Frank-Bemelman/radioglobe-esp32-2025/source/squareline/assets/worldmap_bw_360x180.png

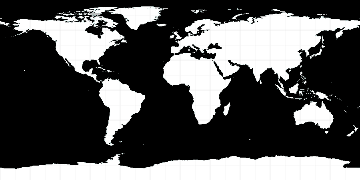
source/squareline/assets/worldmap_bw_360x180.png
