Frank-Bemelman/radioglobe-esp32-2025/source/arduino/RadioGlobe-Display-V4/LVGL_Driver.cpp

/*****************************************************************************
  | File        :   LVGL_Driver.c
  
  | help        : 
    The provided LVGL library file must be installed first
******************************************************************************/
#include "LVGL_Driver.h"

//lv_disp_drv_t disp_drv;
lv_disp_drv_t* disp_drv_ptr = NULL;
// uint8_t disp_drv_safety_buffer[64]; // Dit vangt elke mogelijke overflow gegarandeerd op - ik vertrouw disp_drv niet -> eruit, nu eea weer goed loopt - als extra check of dit verschil maakte

static lv_disp_draw_buf_t draw_buf;
void* buf1 = NULL;
void* buf2 = NULL;
// static lv_color_t buf1[ LVGL_BUF_LEN ];
// static lv_color_t buf2[ LVGL_BUF_LEN ];
// static lv_color_t* buf1 = (lv_color_t*) heap_caps_malloc(LVGL_BUF_LEN, MALLOC_CAP_SPIRAM);
// static lv_color_t* buf2 = (lv_color_t*) heap_caps_malloc(LVGL_BUF_LEN, MALLOC_CAP_SPIRAM);
    
lv_disp_drv_t *current_disp_drv = NULL; // 28JUL26 20:23

/* Serial debugging */
void Lvgl_print(const char * buf)
{
    // Serial.printf(buf);
    // Serial.flush();
}

/*  Display flushing 
    Displays LVGL content on the LCD
    This function implements associating LVGL data to the LCD screen
*/
void Lvgl_Display_LCD( lv_disp_drv_t *disp_drv, const lv_area_t *area, lv_color_t *color_p )
{ // 28JUL26 20:23 store current driver for VSYNC callback usage
  current_disp_drv = disp_drv; 
  
  // 28JUL26 20:53 replace LCD_addWindow for official esp recommendations
  esp_lcd_panel_draw_bitmap(panel_handle, area->x1, area->y1, area->x2 + 1, area->y2 + 1, color_p);
  
  // 28JUL26 20:53 commented out
  // LCD_addWindow(area->x1, area->y1, area->x2, area->y2, (uint8_t *)color_p);


  
  // 28JUL26 20:23moved to example_on_vsync_event
  //lv_disp_flush_ready( disp_drv );
}
/*Read the touchpad*/
void Lvgl_Touchpad_Read( lv_indev_drv_t * indev_drv, lv_indev_data_t * data )
{
  Touch_Read_Data();
  if (touch_data.points != 0x00) {
    data->point.x = touch_data.x;
    data->point.y = touch_data.y;
    data->state = LV_INDEV_STATE_PR;
// FRANK disabled    printf("LVGL : X=%u Y=%u points=%d\r\n",  touch_data.x , touch_data.y,touch_data.points);
  } else {
    data->state = LV_INDEV_STATE_REL;
  }
  if (touch_data.gesture != NONE ) {    
  }
  touch_data.x = 0;
  touch_data.y = 0;
  touch_data.points = 0;
  touch_data.gesture = NONE;
}
void example_increase_lvgl_tick(void *arg)
{
    /* Tell LVGL how many milliseconds has elapsed */
    lv_tick_inc(EXAMPLE_LVGL_TICK_PERIOD_MS);
}
void Lvgl_Init(void)
{
  lv_init();
  esp_lcd_rgb_panel_get_frame_buffer(panel_handle, 2, &buf1, &buf2);                                          
  lv_disp_draw_buf_init( &draw_buf, buf1, buf2, ESP_PANEL_LCD_WIDTH * ESP_PANEL_LCD_HEIGHT);           

  /*Initialize the display*/
  disp_drv_ptr = (lv_disp_drv_t*)malloc(sizeof(lv_disp_drv_t));
  lv_disp_drv_init(disp_drv_ptr);
  //lv_disp_drv_init( &disp_drv );
  
  /*Change the following line to your display resolution*/
  disp_drv_ptr->hor_res = LCD_HEIGHT;
  disp_drv_ptr->ver_res = LCD_WIDTH;
  disp_drv_ptr->flush_cb = Lvgl_Display_LCD;
  disp_drv_ptr->full_refresh = 1;                    /**< 1: Always make the whole screen redrawn*/
  disp_drv_ptr->draw_buf = &draw_buf;

  
  //disp_drv.hor_res = LCD_HEIGHT;
  //disp_drv.ver_res = LCD_WIDTH;
  //disp_drv.flush_cb = Lvgl_Display_LCD;
  //disp_drv.full_refresh = 1;                    /**< 1: Always make the whole screen redrawn*/
  //disp_drv.draw_buf = &draw_buf;

  lv_disp_drv_register(disp_drv_ptr);
  //lv_disp_drv_register( &disp_drv );

  /*Initialize the (dummy) input device driver*/
  static lv_indev_drv_t indev_drv;
  lv_indev_drv_init( &indev_drv );
  indev_drv.type = LV_INDEV_TYPE_POINTER;
  indev_drv.read_cb = Lvgl_Touchpad_Read;
  lv_indev_drv_register( &indev_drv );

  /* Create simple label */
  lv_obj_t *label = lv_label_create( lv_scr_act() );
  lv_label_set_text( label, "Hello Ardino and LVGL!");
  lv_obj_align( label, LV_ALIGN_CENTER, 0, 0 );

  const esp_timer_create_args_t lvgl_tick_timer_args = {
    .callback = &example_increase_lvgl_tick,
    .name = "lvgl_tick"
  };
  esp_timer_handle_t lvgl_tick_timer = NULL;
  esp_timer_create(&lvgl_tick_timer_args, &lvgl_tick_timer);
  esp_timer_start_periodic(lvgl_tick_timer, EXAMPLE_LVGL_TICK_PERIOD_MS * 1000);

}

extern SemaphoreHandle_t lvgl_mutex;

void Lvgl_Loop(void)
{ if (xSemaphoreTake(lvgl_mutex, pdMS_TO_TICKS(50)) == pdTRUE)  // maybe not - crashes worldmap when touched multiple times
  { lv_timer_handler(); /* let the GUI do its work */
    xSemaphoreGive(lvgl_mutex); // Geef de sleutel direct weer terug
  }
  vTaskDelay(pdMS_TO_TICKS(1)); // let's try again 21JUL26
}
