Frank-Bemelman/radioglobe-esp32-2025/source/arduino/RadioGlobe-Display-V4/database.ino

// functions for database of radio stations
// makes use of stations.json file stored on SD card

#include "FS.h"
#include "SD_MMC.h"
#include "database.h"
#include "countrycodes.h"

#include <ctype.h>


bmpfile StationsMap;  // to maintain a quick lookup map of available directories     
//bmpfile NauticMap;    // to have a map of water vs land that have actual timezones according to google
stations_arraybin Stations;



char rolldata[(64+2)*MAX_STATIONS];


void listDir(fs::FS &fs, const char *dirname, uint8_t levels) {
  Serial.printf("Listing directory: %s\n", dirname);

  File root = fs.open(dirname);
  if (!root) {
    Serial.println("Failed to open directory");
    return;
  }
  if (!root.isDirectory()) {
    Serial.println("Not a directory");
    return;
  }

  File file = root.openNextFile();
  while (file) {
    if (file.isDirectory()) {
      Serial.print("  DIR : ");
      Serial.println(file.name());
      if (levels) {
        listDir(fs, file.path(), levels - 1);
      }
    } else {
      Serial.print("  FILE: ");
      Serial.print(file.name());
      Serial.print("  SIZE: ");
      Serial.println(file.size());
    }
    file = root.openNextFile();
  }
}



// REBUILD DATABASE BUTTON
void RebuildDatabase(lv_event_t * e)
{ if(isLongPressed(e)==5)
  { beepforMs(1000);
    bCheckDatabase = true;
  }
}

// create a directory structure per NS degree and EW degree
// in theory 64800 files to store
// ./N/N<digit/10>/<digit%10>/E<digit/10>/<digit%10>
// ./N/N<digit/10>/<digit%10>/W<digit/10>/<digit%10>
// ./S/S<digit/10>/<digit%10>/E<digit/10>/<digit%10>
// ./S/S<digit/10>/<digit%10>/W<digit/10>/<digit%10>
// each directory containing filenames like N24W25urls.txt containing list of stations for that coordinate

void BuildDatabaseNow(void)
{ uint16_t timeout = 5;
  char content[128];
  char filename[32];

  Serial.printf("BuildDatabaseNow()\n");

  lv_label_set_text(ui_Database_Output_File, "");
  lv_obj_clear_flag(uic_RebuildDatabase, LV_OBJ_FLAG_HIDDEN);
  lv_obj_clear_flag(uic_RebuildDatabaseButtonText, LV_OBJ_FLAG_HIDDEN);
  lv_obj_add_state(uic_RebuildDatabase, LV_STATE_DISABLED);
  lv_obj_add_flag(uic_HomeButton3, LV_OBJ_FLAG_HIDDEN);
  //lv_label_set_text(ui_MapBanner, "All\nThose\nBeautiful\nInternet\nRadio\nStations\nAround\nThe\nWorld\n");

  if(Puck_SD_GB == 0)
  { lv_label_set_text(ui_Database_Dir_Path, "No SD Card Found!");
    lv_refr_now(NULL); 
    delay(1000);
    while(timeout)
    {  delay(1000);
       sprintf(content, "leaving in %d seconds", timeout);
       lv_label_set_text(ui_Database_Dir_Path, content);
       lv_refr_now(NULL); 
       timeout --;
    }
    delay(1000);
    lv_scr_load(ui_Home); 
    lv_label_set_text(ui_Database_Dir_Path, "");
  }
  else
  { lv_label_set_text(ui_Database_Dir_Path, "SD Card Found!");
    lv_refr_now(NULL); 
    strcpy(filename, "/stations150K.json"); // don't fortget the forward slash
    ReadDatabase(SD_MMC, filename); // don't fortget the forward slash
    WriteStationsBitmapFile(SD_MMC, "/stationsmap.bmp");
    Serial.println("Database rebuild done");
  }
  Serial.println("End BuildDatabaseNow()");
  bCheckDatabase = false;
}

void ReadDatabase(fs::FS &fs, char *filename)
{ char sometext[128];
  char oneline[128];
  char outputfilename[64];
  char dirpath[64];
  char *p;
  size_t bytesread;
  uint32_t filesize = 0;
  uint32_t fileposition = 0;
  uint16_t percentagedone;
  uint32_t startMillis = millis();  
  uint32_t currentMillis;
  uint16_t parsefase = 0;
  uint32_t urlcount = 0;
  uint32_t filecount = 0;
  float floatn;
  float floate;
  int16_t ns=0;
  int16_t ew=0;
  File urls;

  if(1)
  { File root = fs.open(filename, FILE_READ);
    if (!root) 
    { sprintf(sometext, "Failed To Open %s", filename);
      lv_label_set_text(ui_Database_Dir_Path, sometext);
      lv_refr_now(NULL);
      Serial.println(sometext);
      delay(2000); 
      lv_obj_clear_state(uic_RebuildDatabase, LV_STATE_DISABLED);
      lv_obj_clear_flag(uic_HomeButton3, LV_OBJ_FLAG_HIDDEN);
      return;
    }
    sprintf(sometext, "Succes opening %s", filename);
    lv_label_set_text(ui_Database_Dir_Path, sometext);
    lv_refr_now(NULL); 
    delay(2000); 
  
    filesize = root.size(); // used for progress percentage calculation
    // Serial.printf("filesize of %s is %ld\n", filename, filesize);

    lv_obj_set_pos(uic_MapCursor, ew, -ns);
    // Start the animation on the map
    //lv_obj_clear_state(uic_MapBanner, LV_STATE_DISABLED);
    lv_obj_clear_state(uic_MapCursor, LV_STATE_DISABLED);

    // invalidate map red dots, make it blank
    memset(StationsMap.pixeldata, 0x0, sizeof(StationsMap.pixeldata));

    while(root.available())//  && urlcount < 500)
    { bool UpdateGrapics;
      currentMillis = millis();
      if (currentMillis - startMillis >= 1000)  // every 5S screen update
      { startMillis = currentMillis;
        UpdateGrapics = true;
        fileposition = root.position();
        percentagedone = fileposition * 100 / filesize;
        sprintf(sometext, "Done %d%% urls=%ld", percentagedone, urlcount);
        lv_label_set_text(ui_Database_Progress, sometext);
        lv_refr_now(NULL); 
      }

      bytesread = root.readBytesUntil(0x0a, oneline, sizeof(oneline)-1);
      oneline[bytesread]=0;
      //Serial.printf("bytesread= %d lineread = %s\n", bytesread, oneline);
      switch(parsefase)
      { case 0:
          if((p = strstr(oneline, "\": {")) != NULL) // city,country
          { // example
            //    "Winston-Salem,US": {
            // results in: Winston-Salem_US.txt  
            if((p=strchr(oneline, '\"'))!=NULL)
            { strcpy(outputfilename, p+1);
              if((p=strchr(outputfilename, '\"')) != NULL)*p=0;
              if((p=strchr(outputfilename, ',')) != NULL)*p='_';
              // seen a city, country entry like this "Biel/Bienne,CH": {
              // which causes havoc when filesystem sees this as a directory path
              // fix by replacing the / for a -
              if((p=strchr(outputfilename, '/')) != NULL)*p='-';
              strcat(outputfilename, ".txt");
              Serial.println(outputfilename);
            }
            else strcpy(outputfilename, "noname.txt");
            parsefase = 1;
          }
          break;
        case 1:
          if((p = strstr(oneline, "\"n\": ")) != NULL)
          { //Serial.println(p);
            sscanf(&p[5], "%f", &floatn);
            if(floatn>0)ns=(int)(floatn+0.5);
            else ns=(int)(floatn-0.5);
            parsefase = 2;
          }        
          break;
        case 2: // create directory
          if((p = strstr(oneline, "\"e\": ")) != NULL)
          { //Serial.println(p);
            sscanf(&p[5], "%f", &floate);
            if(floate>0)ew=(int)(floate+0.5);
            else ew=(int)(floate-0.5);
            sprintf(dirpath, "/%c/%d/%d/%c/%d/%d", (ns<0)?'S':'N', abs(ns)/10, abs(ns)%10, (ew<0)?'W':'E', abs(ew)/10, abs(ew)%10);
            //Serial.println(dirpath);
            CreateAllDirInPath(fs, dirpath);
            SetPixelInMap(ns, ew);
            if(UpdateGrapics)lv_obj_set_pos(uic_MapCursor, ew, -ns);
            parsefase = 3;
          }
          break;
        case 3:  // create file
          if((p = strstr(oneline, "\"urls\": [")) != NULL) // start of list
          { sprintf(sometext, "Folder %s", dirpath);
            if(UpdateGrapics)lv_label_set_text(ui_Database_Dir_Path, sometext);
            if(UpdateGrapics)lv_label_set_text(ui_Database_Output_File, outputfilename);
            sprintf(sometext, "/%s/%s", dirpath, outputfilename);
            // SD_MMC.remove(sometext); // delete old file
            urls = SD_MMC.open(sometext, FILE_WRITE);
            filecount++;
            parsefase = 4;
          }
          break;
        case 4:  
          if((p = strstr(oneline, "\"name\": ")) != NULL) // name found
          { //Serial.println(p);
            urls.println(p);  // write name to file 
            parsefase = 5;
          }
          if((p = strstr(oneline, "]")) != NULL) // end of file reached
          { //Serial.println(p);
            urls.close();
            parsefase = 0;
          }
          break;
        case 5:  
          if((p = strstr(oneline, "\"url\": ")) != NULL) // url found
          { //Serial.println(p);
            urls.println(p);  // write to file 
            parsefase = 6;
          }
          break;
        case 6:  
          sprintf(sometext, "\"gps\": \"%f,%f\"", floatn, floate); // write gps to file
          urls.println(sometext);  
          urlcount++;
          parsefase = 4;
          break;

        default:
          break;  
      }
    }  

    urls.close();
    root.close();
    //lv_obj_add_state(uic_MapBanner, LV_STATE_DISABLED); 
    lv_obj_add_state(uic_MapCursor, LV_STATE_DISABLED); 

    percentagedone = 100;
    sprintf(sometext, "Done %d%% urls=%ld", percentagedone, urlcount);
    lv_label_set_text(ui_Database_Progress, sometext);
    sprintf(sometext, "%d Locations Created", filecount);
    lv_label_set_text(ui_Database_Dir_Path, sometext);
    lv_refr_now(NULL); 

  }

   //tellme();

  lv_obj_clear_state(uic_RebuildDatabase, LV_STATE_DISABLED);
  lv_obj_clear_flag(uic_HomeButton3, LV_OBJ_FLAG_HIDDEN);
  
  Serial.println("Database rebuild completed!");
}



void CreateAllDirInPath(fs::FS &fs, char *path) 
{ char pathcopy[64];
  char *s;
  char *d;
  File root;
  s = path;
  d = pathcopy;

  

  //Serial.printf("Create these directories %s\n", path);
  *d++ = *s++; // copy first '/'
  while(*s)
  { while(*s)
    { *d++ = *s++; // copy intil '/' found
      if(*s == '/')
      { break;
      }
    }
    *d = 0; // terminate string

    //Serial.printf("Full path %s\n", path);
    //Serial.printf("Try to open directory %s!\n", pathcopy);
    root = fs.open(pathcopy);
    if(!root) 
    { //Serial.printf("Failed to open directory %s so make it!\n", pathcopy);
      if(SD_MMC.mkdir(pathcopy))
      { //Serial.printf("%s created\n", pathcopy);
      }
      //else Serial.printf("%s creation error\n", pathcopy);
    }
    *d = *s; // *s is '/' in case more directories todo
    // Serial.printf("*s = %d\n", (int)*s);
  }
}      

#define EXPAND_STOP 10 // was 45 - original radioglobe by Jude Pullen uses 2 degrees expansion, too small imo
bool SnapToNearestStation(int16_t for_ns, int16_t for_ew, int16_t *to_ns, int16_t *to_ew, uint16_t hit_count)
{ // convert/round to whole degrees to be used for finding a position with an existing directory path and station file
  int16_t ns;
  int16_t ew;
  int16_t expand;
  int16_t try_ns;
  int16_t try_ew;
  int16_t try_ltx;
  int16_t try_lty;
  int16_t try_rbx;
  int16_t try_rby;
  uint16_t match_count = 0;
  int16_t expand_stop;

  
  ns = for_ns;
  ew = for_ew;
  
  Serial.printf("[Database.ino ~ 352] SnapToNearestStation NS = %d  EW = %d\n", ns, ew);
  if(DisplaySettings.expand_search>100)DisplaySettings.expand_search=100;
  expand_stop = DisplaySettings.expand_search+1;
  Serial.printf("expand_stop = %d\n", expand_stop);
  
  // start at the exact position
  // expand as needed by 1 degree
  // hit_count parameter to find 1st or 2nd or 3rd pixel in map
  // to be used if 1st or next pixel gives a dissapointing small amount of stations

  try_ns = ns;
  try_ew = ew;
  expand = 0;

  
  while((expand < expand_stop) && (match_count!=hit_count))
  { // define the square to scan
    try_lty = ns - expand;
    try_ltx = ew - expand;
    try_rby = ns + expand;
    try_rbx = ew + expand;

    if(TestPixelInMap(try_ns, try_ew) && match_count==0)
    { match_count++;
      expand++;
    }
    else // loop around
    { try_ns = try_lty; 
      try_ew = try_ltx; 
      while(try_ew<try_rbx && (match_count!=hit_count)) // go right 
      { try_ew++;
        if(TestPixelInMap(try_ns, try_ew))
        { match_count++;
        }  
      }
      while(try_ns<try_rby && (match_count!=hit_count)) // go down 
      { try_ns++;
        if(TestPixelInMap(try_ns, try_ew))
        { match_count++;
        }  
      }
      while(try_ew>try_ltx && (match_count!=hit_count)) // go left 
      { try_ew--;
        if(TestPixelInMap(try_ns, try_ew))
        { match_count++;
        }  
      }
      while(try_ns>try_lty && (match_count!=hit_count)) // go up 
      { try_ns--;
        if(TestPixelInMap(try_ns, try_ew))
        { match_count++;
        }  
      }
      expand++;
    }
  }

  if(expand >= expand_stop)
  { Serial.printf("No station with expand %d -> NS -> %d WE -> %d\n", expand, try_ns, try_ew);
    return false; 
  }
  Serial.printf("Stations found within expand %d -> NS -> %d WE -> %d\n", expand, try_ns, try_ew);
  *to_ns = try_ns;
  *to_ew = try_ew;
  return true;
}


// find stations at current calibrated position
int32_t search_mS;
void FindNewStation(void)
{ bool dirscan = true;
  bool dirfound = false;
  int16_t ns;
  int16_t ew;
  int16_t dir_ns;
  int16_t dir_ew;
  int16_t center;
  char oneline[128];
  size_t bytesread;
  char *p;

  // results from SnapToNearestStation()
  bool mapfind = false;
  int16_t mapfind_ns;
  int16_t mapfind_ew;

  char dirpath[64];
  File root;
  File file;
  char content[64];
  
  
  search_mS = 0;
 
  // convert to whole degrees to be used for finding directory path to url file
  ns = (DataFromDisplay.ns_cal+5)/10; // from tenths of degrees to whole degrees
  ew = (DataFromDisplay.ew_cal+5)/10; // from tenths of degrees to whole degrees

  Stations.count = 0;
  Stations.requested -1;
  char firstcountrycode[3] = ""; // near borders, different countries can be in the directory, decided to stick with the country first found, to avoid a mixed list

  lv_label_set_text(ui_Station_Name, "");
  lv_label_set_text(ui_Home_City, "");
  lv_obj_add_flag(ui_Home_Flag, LV_OBJ_FLAG_HIDDEN); 
  lv_label_set_text(ui_Home_Country, "");
  // also on clock, in case we play the globe while clock is shown
  lv_obj_add_flag(ui_ClockFlag, LV_OBJ_FLAG_HIDDEN); 
  lv_label_set_text(ui_Clock_Country, "");
  lv_refr_now(NULL); // show immediately
  

  search_mS = millis();

  //nieuw, probeer minimaal 10 stations te vinden, blijf witte pixels zoeken
  uint16_t hitcount = 0;
  while(Stations.count < 10 && hitcount<10)
  { hitcount++;
    mapfind = SnapToNearestStation(ns, ew, &mapfind_ns, &mapfind_ew, hitcount);
    if(mapfind == 0)
    { // game over
      break;
    }
    CollectStationsAtGps(mapfind_ns, mapfind_ew, firstcountrycode);
    Serial.printf("Collecting Attempt %d gave %d stations in %ld mS\n", hitcount, Stations.count, (millis() - search_mS));
  }

  
  Serial.printf("End search -> %ld\n", millis() - search_mS);
  
  if(Stations.count)
  { //sprintf(content, "%d Stations Found", Stations.count);
    //lv_label_set_text(ui_Station_Name, content);
    
    AddToQueueForGlobe("Reset Your DataFromGlobe.D_QueueStationIndex to -1", MESSAGE_NEW_LIST_LOADED);
    
    // pick a random station from the list
    uint16_t random_station; 
    random_station = random(0,Stations.count);
    
    Stations.connect_attempts = 0;
    //ForceGlobeStationGPSupdate = true; 
    //AddStationToQueueForGlobe(random_station);
  }  
  else
  { lv_label_set_text(ui_Station_Name, "No Stations Found");
    // normally, timezone is requested for the station that is requested
    // if no stations are found, set the timezone according to the coordinates from the globe
    Stations.requested = -1; 
    AddStationToQueueForGlobe(-1); // no new station to play really, but will trigger timezone/geolocation requests
  }

  // dump to serial port
  //for(int n = 0; n<Stations.count; n++)
  //{ Serial.printf("[%d] N=%s\nU=%s\n", n, Stations.StationNUG[n].name, Stations.StationNUG[n].url);
  //}

  Stations.connect_attempts = 0;
  ScrollNeedsReload = true;
}

void CollectStationsAtGps(int16_t mapfind_ns, int16_t mapfind_ew, char *firstcountrycode)
{ File root;
  File file;
  char dirpath[64];
  char content[64];
  int16_t dir_ns;
  int16_t dir_ew;
  char oneline[128];
  size_t bytesread;
  char *p;
  char town[32] = "";
  char countrycode[3] = "";
  char countryname[50] ="";
        

  
  if(Puck_SD_GB)
  { dir_ns = mapfind_ns;
    dir_ew = mapfind_ew;
    sprintf(dirpath, "/%c/%d/%d/%c/%d/%d", (dir_ns<0)?'S':'N', abs(dir_ns)/10, abs(dir_ns)%10, (dir_ew<0)?'W':'E', abs(dir_ew)/10, abs(dir_ew)%10);
    Serial.println(dirpath);
    //lv_label_set_text(ui_Station_Title, dirpath);
    //lv_refr_now(NULL); 

    root = SD_MMC.open(dirpath);
    if (!root) 
    { Serial.println("Failed to open directory");
      return;
    }
    
    file = root.openNextFile();

    while (file) 
    { if(!file.isDirectory()) 
      { //Serial.print("STATIONS FILE: ");
        //Serial.print(file.name());
        //Serial.print(" FILE SIZE: ");
        //Serial.println(file.size());

        // while (file && Stations.count<(MAX_STATIONS-1))
        // dit gaat op tilt, met name bij de reload scroll als meer dan ?? stations, zeker geen 100 of 150 mogelijk 
        // dus even naar 25 max

        Serial.printf("File with stations (=%d) opened in %ld mS\n", Stations.count, (millis() - search_mS));

        if (Stations.count >= MAX_STATIONS) 
        { file.close();
          break; // done, get out og here
        }
        
        if(Stations.count==0)
        { lv_label_set_text(ui_Station_Title, file.name());
          lv_refr_now(NULL); 
        }  
        
        strcpy(town, file.name());
        // filenames are constructed from name of town, underscore, and 2 letter country code, like -> Amsterdam_NL.txt
        if((p=strchr(town, '_')) != NULL)
        { *p++ = 0;
          //Serial.printf("sizeof(Countrylist) = %ld\n", sizeof(CountryList) / sizeof(country_info));
          strncpy(countrycode, p, 2);
          countrycode[2]=0;

          if(strlen(firstcountrycode) == 0)strcpy(firstcountrycode, countrycode);

          if(!FindCountryNameByCode(countryname, countrycode))
          { Serial.printf("Not a valid countrycode %s !!!!!!!!!!!!!!!\n", countrycode);
          }
          Serial.printf("Found country: <%s>\n", countryname);
        }


        if(strcmp(firstcountrycode, countrycode) == 0) // same country
        {
          while(file.available() && Stations.count<MAX_STATIONS)
          { bytesread = file.readBytesUntil(0x0a, oneline, sizeof(oneline)-1);
            oneline[bytesread]=0;
            if((p = strrchr(oneline, '\"')) != NULL)*p=0; // get rid of the last "
            // Serial.println(oneline);
            if((p = strstr(oneline, "\"name\": \"")) != NULL)
            { // example:  "name": "Dr P4 Syd"
              // Serial.println(p+9);
              p+=9; // jump forward to start of name
              *(p+31)=0; 
              strcpy(Stations.StationNUG[Stations.count].name, p);
            }  
            else if((p = strstr(oneline, "\"url\": \"")) != NULL)
            { // example:  "url": "https://stream.radio-fratz.de/stream_high.mp3"
              // Serial.println(p+8);
              p+=8; // jump forward to start of url
              strcpy(Stations.StationNUG[Stations.count].url, p);
            }  
            else if((p = strstr(oneline, "\"gps\": \"")) != NULL)
            { // Serial.println(p+8);
              p+=8; // jump forward to start of gps coordinates
              sscanf(p, "%f,%f", &Stations.StationNUG[Stations.count].gps_ns, &Stations.StationNUG[Stations.count].gps_ew);

              strcpy(Stations.StationNUG[Stations.count].town, town);
              strcpy(Stations.StationNUG[Stations.count].countrycode, countrycode);
              strcpy(Stations.StationNUG[Stations.count].countryname, countryname);

              // play first one found, for snappy feeling
              if(Stations.count==0)
              { ForceGlobeStationGPSupdate = true; 
                AddStationToQueueForGlobe(Stations.count);
                while(ToGlobe.QueueCnt)loop_esp_now(); // send everything out immediately 
              }  

              // in all honesty, ignore if country not the same as first one found and also ignore this url if already in list
              if(strcmp(firstcountrycode, countrycode) == 0) // same country
              { //Serial.printf("%s same as %s\n", firstcountrycode, countrycode);
                if(CheckIfUniqueUrl())
                { Stations.count++;
                  Serial.printf("Station %d (country %s )found in %ld mS\n", Stations.count, Stations.StationNUG[Stations.count].countryname, (millis() - search_mS));
                }  
              }
              else
              { Serial.printf("%s differs from %s\n", firstcountrycode, countrycode);
              }
            }
          } 
        }
      }
      file.close();
      file = root.openNextFile();
    } 
    root.close();
  }
}

bool CheckIfUniqueUrl(void)
{ uint16_t idx=0;
  if(!Stations.count)return true;
  while(idx<Stations.count)
  { if(strcmp(Stations.StationNUG[Stations.count].url, Stations.StationNUG[idx].url)==0)return false; // url already in list of stations
    idx++;
  }
  return true;
}

void SetPixelInMap(int16_t ns, int16_t ew)
{ // ew varies between -180 and 180
  // -180 to be stored in [359]
  ew += 180;  // convert -180 to 179 range to 0-359
  ns += 90;   // convert -90 to 90 range to 0-180
  if(ns>179)ns=179;
  if(ew>359)ew-=360;
  StationsMap.pixeldata[((180-ns)*48)+(ew/8)] |= 0x80>>(ew%8); //48 bytes, rounded up from 45 to get a 4-byte multiple
}

bool TestPixelInMap(int16_t ns, int16_t ew)
{ // ew varies between -180 and 179
  // ns varies between 90 and -89
  // -180 to be stored in [359]
  ew += 180;  // convert -180 to 179 range to 0-359
  ns += 90;   // convert -90 to 90 range to 0-180
  if(ns>179)ns=179;
  if(ew>359)ew-=360;
  if(ns<1)return false;
  if(ew<1)return false;
  
  //Serial.printf("Pixeltest ns=%d ew=%d %02X vs %02X\n", ns, ew, (uint16_t)StationsMap.pixeldata[((180-ns)*48)+(ew/8)], (uint16_t)(0x80>>(ew%8)));
  if(StationsMap.pixeldata[((180-ns)*48)+(ew/8)] & (0x80>>(ew%8)))return true;
  return false;
}



void tellme(void)
{ Serial.println(StationsMap.bmpheader.filler);
  Serial.println(StationsMap.bmpheader.type);
  Serial.println(StationsMap.bmpheader.size);
  Serial.println(StationsMap.bmpheader.reserved1);
  Serial.println(StationsMap.bmpheader.reserved2);
  Serial.println(StationsMap.bmpheader.offset);
  Serial.println(StationsMap.bmpheader.dib_header_size);
  Serial.println(StationsMap.bmpheader.width_px);
  Serial.println(StationsMap.bmpheader.height_px);
  Serial.println(StationsMap.bmpheader.num_planes);
  Serial.println(StationsMap.bmpheader.bits_per_pixel);
  Serial.println(StationsMap.bmpheader.compression);
  Serial.println(StationsMap.bmpheader.image_size_bytes);
  Serial.println(StationsMap.bmpheader.x_resolution_ppm);
  Serial.println(StationsMap.bmpheader.y_resolution_ppm);
  Serial.println(StationsMap.bmpheader.num_colors);
  Serial.println(StationsMap.bmpheader.important_colors);

  int n;
  int w;
  for(n=0;n<180;n++)
  { for(w=0;w<45;w++)
    { Serial.printf("%02x", (uint16_t)StationsMap.pixeldata[(n*48)+w]); //48 bytes, rounded up from 45 to get a 4-byte multiple
    }
    Serial.printf("\n");
  }
}


static uint32_t startMillis;
static uint32_t currentMillis;


void RadioGlobeClick(lv_event_t * e)
{ int16_t clicktime;
  lv_event_code_t event_code = lv_event_get_code(e);

  clicktime = isLongPressedV2(e);
  //Serial.printf("RadioGlobeClick() clicktime = %d\n", clicktime);
  
  if(clicktime==0) // normal click
  { if(!bMusicMode)
    { Serial.printf("!bMusicMode RadioGlobeClick() Stations.count = %d\n", Stations.count);
      if(Stations.count == 0)
      { SetFlag("xxxx");
        lv_obj_add_flag(uic_Home_City, LV_OBJ_FLAG_HIDDEN); // hide city name until new country code is received
        lv_obj_add_flag(uic_Home_Country, LV_OBJ_FLAG_HIDDEN); // hide country name until new country code is received

        //lv_label_set_text(ui_Station_Name, "Searching..."); // pointless, searching goes so fast you won't see this
        lv_label_set_text(ui_Station_Title, "");
        lv_obj_add_flag(ui_ledconnect, LV_OBJ_FLAG_HIDDEN); 
        lv_refr_now(NULL); 
        FindNewStation();
        ReloadScroll();
      }
    }
    else
    { //Serial.printf("bMusicMode RadioGlobeClick() Stations.count = %d\n", Stations.count);
      ReloadScroll();
    }
    beepforMs(50);
    lv_scr_load(ui_StationSelectScreen);
    startMillis = millis(); 
    Serial.printf("RadioGlobeClick() return\n");
  }  

  if(clicktime==5 && DisplaySettings.globe_sd_gb!=0) // long press, toggle between radio/music mode
  { //Serial.printf("RadioGlobeClick clicktime==5 LV_EVENT_LONG_PRESSED_REPEAT \n");
    if(!bMusicMode)
    { //Serial.printf("Radio -> Music Mode LV_EVENT_LONG_PRESSED_REPEAT \n");
      beepforMs(50);
      SetLed(0,0); SetLed(1,0); SetLed(2,0); SetLed(3,0);
      lv_label_set_text(ui_Station_Name, "");
      lv_label_set_text(ui_Status_Line, "READING SD CARD");
      lv_label_set_text(ui_Station_Title, "");
      lv_obj_add_flag(ui_ledconnect, LV_OBJ_FLAG_HIDDEN); 
      AddToQueueForGlobe("", MESSAGE_GLOBE_PLAY_SD); // instructs the globe to prepare a list of songs from the SD card
      lv_obj_clear_flag(ui_Jukebox, LV_OBJ_FLAG_HIDDEN);
      lv_obj_add_flag(ui_Home_City, LV_OBJ_FLAG_HIDDEN); 
      lv_obj_add_flag(ui_Home_Flag, LV_OBJ_FLAG_HIDDEN); 
      lv_obj_add_flag(ui_Home_Country, LV_OBJ_FLAG_HIDDEN);


      bMusicMode = true;
    } 
    else
    { // back to radio
      //Serial.printf("Music -> Radio Mode LV_EVENT_LONG_PRESSED_REPEAT \n");
      lv_obj_add_flag(ui_Jukebox, LV_OBJ_FLAG_HIDDEN);
      beepforMs(50);
      bMusicMode = false;
      FindNewStation();
      ReloadScroll();
    } 
  }
}

void ReloadScroll(void)
{ uint16_t len;
  uint16_t space;
  uint16_t n;
  char *p;

  if(!ScrollNeedsReload)return;
  ScrollNeedsReload = false;
  space = sizeof(rolldata);
  if(bMusicMode)strcpy(rolldata, "No Files");
  else strcpy(rolldata, "No Stations");
  lv_label_set_text(ui_StationRollerSelected, "0-0");
  lv_roller_set_selected(uic_StationRoller, 0, LV_ANIM_ON);

  for(n = 0; n<Stations.count; n++)
  { if((len = strlen(Stations.StationNUG[n].name))>0)
    { //Serial.printf("n=%d space=%d len=%d\n", n, space, len);
      //Serial.printf("N=%s U=%s\n", Stations.StationNUG[n].name, Stations.StationNUG[n].url);
      //Serial.printf("space = %d\n", space);
      if((space-len)>2)
      { if(n==0)
        { p = rolldata;
        }
        else
        { *p++ = '\n'; // end previous line with a newline
        }  
        strcpy(p, Stations.StationNUG[n].name);
        p += len;
        space -= len;         
      }
      else break;
    }
    else break;
  }
  // Serial.println(rolldata);
  // Serial.println(n);

  if(bMusicMode)
  { lv_label_set_text(ui_StationRollerComment, "Playlist From SD-Card"); // usually says connected to station or something
  }
  else 
  { lv_label_set_text(ui_StationRollerComment, ""); 
  }
  
  lv_label_set_text(uic_StationRollerPlace, "");


  lv_roller_set_options(uic_StationRoller, rolldata, LV_ROLLER_MODE_NORMAL);
  if(Stations.count)
  { char content[32];
    if((Stations.requested >=0) && (Stations.requested<Stations.count))
    { sprintf(content, "%d-%d", Stations.requested+1, Stations.count); // top label 1-150 in stations roller
      Serial.printf("lv_roller_set_selected -> %d\n", Stations.requested);
      lv_roller_set_selected(uic_StationRoller, Stations.requested, LV_ANIM_ON);
    }  
    else 
    { sprintf(content, "0-%d", Stations.count); // top label 1-150 in stations roller
      lv_roller_set_selected(uic_StationRoller, 0, LV_ANIM_ON);
    }
    lv_label_set_text(ui_StationRollerSelected, content);
  }
  Serial.printf("Reload Scroll (%d stations) done.\n", Stations.count);
}






void StationScroll(lv_event_t * e)
{ char content[256];
  static uint16_t RollSelection;
  uint16_t index;
  lv_event_code_t event_code = lv_event_get_code(e);

  // events go from PRESSED while scrolling. Stop&Release results in VALUE_CHANGED + CLICKED
  // another short click gives PRESSED+CHANGED+CLICKED

  index = lv_roller_get_selected(uic_StationRoller);
  sprintf(content, "%d-%d", index+1, Stations.count);
  lv_label_set_text(ui_StationRollerSelected, content); 
  
  if(event_code == LV_EVENT_CLICKED) 
  { index = lv_roller_get_selected(uic_StationRoller);
    currentMillis = millis(); 
    if(currentMillis - startMillis > 250)  //test to distuigish between scrolling and clicking
    { RollSelection = index;
    }
    else // short click
    { Serial.printf("index=%d\n", index);
      if(RollSelection == index)
      { if(index < Stations.count) // just check in case
        { Stations.playing = -1;
          Stations.requested = index; 
          if(!bMusicMode)
          { sprintf(content, "Connecting to %s", Stations.StationNUG[Stations.requested].name);
            lv_label_set_text(ui_StationRollerComment, content); 
            Stations.connect_attempts = 0;
            AddStationToQueueForGlobe(Stations.requested);
          }  
          else AddFileToQueueForGlobe(Stations.requested);
        }
        beepforMs(50);
      }  
      RollSelection = index;
    }
  }
  if(event_code == LV_EVENT_PRESSED) 
  { startMillis = millis();  //get the current "time" (actually the number of milliseconds since the program started)
  }
}

uint16_t AddToScroll(char * songartist)
{ char *p;
  char *q;
  uint16_t len;

  if(Stations.count >= 25)return Stations.count;
  //Serial.printf("songartist -> %s\n", songartist);

  strcpy(Stations.StationNUG[Stations.count].url, songartist);

  // get filename part from url
  // example  /GLOBEMUSIC/HT/Emeline_Michel/Emeline_Michel_-_Reine_De_Coeur_-_2008/08_Yon_Ti_Mo.mp3

  //GLOBE SAYS: PLAYLIST_SONG_ARTIST 60 >/GLOBEMUSIC/FR/Pascal Rogé/Poulenc- Chamber Music/03 Sextet for wind quintet & piano in C major- Prestissimo.mp3<
  //songartist has / -> 03 Sextet for wind quintet & piano in C major- Prestissimo
  //songartist without underscores -> 03 Sextet for wind quintet & piano in C major- Prestissimo
  //songartist split at >-< ->  Prestissimo
  //songartist ended with dots if too long Prestissimo

  if((q=strrchr(songartist, '.'))!= NULL)*q=0; // first, terminate at .mp3

  if((p=strrchr(songartist, '/'))!= NULL) // last '/' in string
  { p++; // skip the '/'
    Serial.printf("songartist had / [%s]\n", p);
  }
  else p = songartist; // start at begin again
  
  RemoveUTF8Unprintables(p); // converts to extended ascii where possible (todo make font table extended too)
  
  // now we have the filename without extension 
  // replace underscores with spaces
  for (int i = 0; p[i] != '\0'; i++) 
  { if (p[i] == '_')  p[i] = ' ';
  }
  Serial.printf("songartist without underscores [%s]\n", p);

  if(isdigit(*p) && isdigit(*(p+1)) && *(p+2)==' ')p+=3; // skip the track number if part of songname
  else if( isalpha(*p) && isdigit(*(p+1)) && isdigit(*(p+2)) && *(p+3)=='-')p+=4; // skip the track number of jukebox files
  else if( isdigit(*p) && isdigit(*(p+1)) && isalpha(*(p+2)))p+=2; // skip numbers as 07A
  else if( isdigit(*p) && isdigit(*(p+1)) && isalpha(*(p+2)))p+=2; // skip numbers as 07A
  Serial.printf("songartist initial cleanup -> [%s]\n", p);
  if(*p=='-')p++; // skip leading '-' if any
  if(*p==' ')p++; // skip leading space if any
  
  // if too long, maybe splice if it is format artist - songtitle format
  if(strlen(p)>20)
  { if((q = strchr(p, '-')) != NULL)
    { q++;
      len = strlen(q);
      memmove(p, q, len);
      p[len]=0;
      Serial.printf("songartist split at >-< [%s]\n", p);
    }
  }
  
  // remove leading spaces just in case
  q = p;
  while(*q != 0 && *q == ' ')q++;
  if(q != p)memmove(p, q, strlen(q) + 1);

  // if still too long, mayby end at full word and add three dots
  while((len = strlen(p))>20)
  { if((q=strrchr(p, ' '))!= NULL) // last space in string
    { strcpy(q, "...");
      Serial.printf("shortened [%s] len was %d\n", p, len);
    }
    else break;
  }

  Serial.printf("songartist ended with dots if too long [%s]\n", p);


  strcpy(Stations.StationNUG[Stations.count].name, p);

  Stations.count++;
  ScrollNeedsReload = true;
  return Stations.count;
}

void StationRollPressed(lv_event_t * e)
{ lv_event_code_t event_code = lv_event_get_code(e);
  //Serial.printf("hey->event=%s\n", "StationRollPressed()");
  StationScroll(e);
}

void StationRollVal(lv_event_t * e)
{ lv_event_code_t event_code = lv_event_get_code(e);
  //Serial.printf("hey->event=%s\n", "StationRollVal()");
  StationScroll(e);
}

void StationRollClicked(lv_event_t * e)
{ lv_event_code_t event_code = lv_event_get_code(e);
  //Serial.printf("hey->event=%s\n", "StationRollClicked");
  StationScroll(e);
}

void RollUp(lv_event_t * e)
{ lv_event_code_t event_code = lv_event_get_code(e);
  //Serial.printf("hey->event=%s\n", "RollUp()");
  //StationScroll(e);
}

void RollDown(lv_event_t * e)
{ lv_event_code_t event_code = lv_event_get_code(e);
  //Serial.printf("hey->event=%s\n", "Rolldown()");
  //StationScroll(e);
}



uint16_t PuckApiRequest; // value to check if arriving result can be discarded, as it could perhaps belongs to previous request

void AddStationToQueueForGlobe(int16_t station)
{ // prepare gps position and url for the station we want to hear and get timezone for
  static char lastgpsrequest[32];
  char message[QUEUEMESSAGELENGTH];
  char content[QUEUEMESSAGELENGTH];

  Stations.requested = station; 
  DataFromDisplay.D_RequestedStation = Stations.requested;
  
  if(station < 0) // no actual station to play really, places with no stations, at sea perhaps, but will trigger timezone/geolocation requests
  { // early setting
    lv_label_set_text(uic_Home_City, "");
    lv_label_set_text(uic_Home_Country, "");
    //on map
    sprintf(content, "GPS NS %2.1f - EW %3.1f", (float)DataFromDisplay.ns_cal/10, (float)DataFromDisplay.ew_cal/10);
    lv_label_set_text(ui_Database_GPS_Position, content);
    lv_obj_set_pos(uic_MapCursor, (int)DataFromDisplay.ew_cal/10 - 16, -(int)DataFromDisplay.ns_cal/10); // moved 16 to left, dot is painted left-top corner?
    lv_label_set_text(ui_Database_Output_File, ""); // remove typical "You are in ..." from map
    
    PuckApiRequest++; // value to check if arriving result can be discarded, as it could perhaps belongs to previous request
    sprintf(content, "%d %f %f %d", station, (float)DataFromDisplay.ns_cal/10, (float)DataFromDisplay.ew_cal/10, PuckApiRequest);
    AddToQueueForGlobe(content, MESSAGE_TIMEZONE_NAME); // will use DataFromDisplay.ns_cal, DataFromDisplay.ew_cal as coordinates
    AddToQueueForGlobe(content, MESSAGE_GET_GEOLOCATION); // will use DataFromDisplay.ns_cal, DataFromDisplay.ew_cal as coordinates
    loop_esp_now(); // send it now, before it gets old
    lv_obj_add_flag(ui_Home_Flag, LV_OBJ_FLAG_HIDDEN); // hide flag
    lv_obj_add_flag(ui_PresetFlag, LV_OBJ_FLAG_HIDDEN);
    SetLed(0,0); SetLed(1,0); SetLed(2,0); SetLed(3,0);

    World.gps_ns = (float)DataFromDisplay.ns_cal/10;
    World.gps_ew = (float)DataFromDisplay.ew_cal/10;
    strcpy(World.CountryName, ""); // we don't know where we are
    
  }
  else if(station<MAX_STATIONS+MAX_FAVORITES)
  { bMusicMode = false;
    DataFromDisplay.D_QueueStationIndex = station;
    Stations.playing = -1;

    if(bPowerStatus == true)
    { sprintf(message, "%s-%s", Stations.StationNUG[station].countrycode, Stations.StationNUG[station].url);
      // send countrycode and station url to globe
      AddToQueueForGlobe(message, MESSAGE_START_THIS_STATION);
    }

    lv_label_set_text(ui_Station_Name, Stations.StationNUG[station].name);
    // easy peasy to postion that led at the end of the station name
    lv_obj_add_flag(ui_ledconnect, LV_OBJ_FLAG_HIDDEN); 
    lv_point_t text_end_point;
    lv_label_get_letter_pos(ui_Station_Name, strlen(Stations.StationNUG[station].name), &text_end_point);
    lv_obj_set_x(ui_ledconnect, (text_end_point.x -200) + 12);
    
//    Serial.printf("x=%d\n",text_end_point );                            

    lv_obj_add_flag(ui_FilePlayProgressBar, LV_OBJ_FLAG_HIDDEN); 
    lv_obj_clear_flag(ui_Status_Line, LV_OBJ_FLAG_HIDDEN); 
    lv_label_set_text(ui_Status_Line, "");
    lv_label_set_text(ui_Station_Title, "");
    lv_refr_now(NULL); 

    if(station<MAX_STATIONS)Stations.connect_attempts++;
    DataFromDisplay.D_StationGpsNS = Stations.StationNUG[station].gps_ns;
    DataFromDisplay.D_StationGpsEW = Stations.StationNUG[station].gps_ew;


    Serial.printf(" -----------------  AddStationToQueueForGlobe() station for country <%s>\n", Stations.StationNUG[station].countrycode);

    // if this country code is our own home country, adjust clock mode for that 
    if(strcmp(Stations.StationNUG[station].countrycode, Stations.StationNUG[(MAX_STATIONS+MAX_FAVORITES+MAX_HOMES-1)].countrycode) == 0)
    { bClockHomeTime = true;
      Home.gps_ns = Stations.StationNUG[(MAX_STATIONS+MAX_FAVORITES+MAX_HOMES-1)].gps_ns;
      Home.gps_ew = Stations.StationNUG[(MAX_STATIONS+MAX_FAVORITES+MAX_HOMES-1)].gps_ew;
      World.gps_ns = 10000; // to prevent clockflagtoggle switch to world mode
      World.gps_ew = 10000; // to prevent clockflagtoggle switch to world mode

    }
    else
    { bClockHomeTime = false;
      World.gps_ns = Stations.StationNUG[station].gps_ns;
      World.gps_ew = Stations.StationNUG[station].gps_ew;
    }

    // check if gps position is a new one
    sprintf(content, "%f %f", Stations.StationNUG[station].gps_ns, Stations.StationNUG[station].gps_ew);
    if(strcmp(lastgpsrequest, content) != NULL || (ForceGlobeStationGPSupdate == true))
    { strcpy(lastgpsrequest, content);
      ForceGlobeStationGPSupdate = false;

      // add station and incrementing PuckApiRequest number
      PuckApiRequest++; // value to check if arriving result can be discarded, as it could perhaps belongs to previous request
      sprintf(content, "%d %s %d", station, lastgpsrequest, PuckApiRequest);
      if(bClockHomeTime)AddToQueueForGlobe(content, MESSAGE_HOME_TIMEZONE_NAME);
      else AddToQueueForGlobe(content, MESSAGE_GET_TIMEZONE_BY_GPS);
      AddToQueueForGlobe(content, MESSAGE_GET_GEOLOCATION_BY_GPS);
      loop_esp_now(); // send it now, before it gets old
    }

    Serial.printf("Flag set early by AddStationToQueueForGlobe() = %s\n", Stations.StationNUG[station].countrycode);

    // show immedeately what is known
    // set flags early - possibly corrected later, when globe thinks it is different 
    SetFlag(Stations.StationNUG[station].countrycode);
    if(bClockHomeTime)
    { strcpy(Home.CountryCode, Stations.StationNUG[station].countrycode); // later used for clock face
      // no country name copied, keep the HOME SWEET HOME text
      //strcpy(Home.CountryName, AllUpperCase(Stations.StationNUG[Stations.requested].countryname)); 
    }
    else
    { strcpy(World.CountryCode, Stations.StationNUG[station].countrycode); // later used for clock face
      strcpy(World.CountryName, Stations.StationNUG[station].countryname); // later used for clock face
    }

    lv_obj_clear_flag(ui_ClockFlag, LV_OBJ_FLAG_HIDDEN); // as it was hidden by a new search start
    lv_obj_clear_flag(ui_PresetFlag, LV_OBJ_FLAG_HIDDEN); // as it was hidden by a new search start

    Serial.printf("Town = %s\n", Stations.StationNUG[station].town);
    lv_label_set_text(uic_Home_City, Stations.StationNUG[station].town);

    Serial.printf("Country = %s\n", Stations.StationNUG[station].countryname);
    lv_label_set_text(uic_Home_Country, Stations.StationNUG[station].countryname);
    lv_label_set_text(uic_Clock_Country, Stations.StationNUG[station].countryname);


    // show if volume not a zero
    if(DataFromDisplay.volumevalue)
    { lv_obj_clear_flag(ui_Home_Flag, LV_OBJ_FLAG_HIDDEN); // as it was hidden by a new search start
      lv_obj_clear_flag(uic_Home_City, LV_OBJ_FLAG_HIDDEN); // it was hidden by a new search start
      lv_obj_clear_flag(uic_Home_Country, LV_OBJ_FLAG_HIDDEN); // it was hidden by a new search start
    }

    lv_obj_clear_flag(uic_Clock_Country, LV_OBJ_FLAG_HIDDEN); // unhide country name 

    // also update the world map screen
    sprintf(content,"Greetings From  %s", GetAllUpperCase(message, Stations.StationNUG[station].countryname));
    lv_label_set_text(ui_Database_Town_Name, content);
    lv_label_set_text(ui_Database_Progress, ""); // erase exchange currency and rate
    lv_obj_set_pos(uic_MapCursor, (int)Stations.StationNUG[station].gps_ew - 16, -(int)Stations.StationNUG[station].gps_ns); // moved 16 to left, dot is painted left-top corner?
    sprintf(content, "GPS NS %2.4f - EW %3.4f", Stations.StationNUG[station].gps_ns, Stations.StationNUG[station].gps_ew);
    lv_label_set_text(ui_Database_GPS_Position, content);
    sprintf(content,"You Are In  %s", Stations.StationNUG[station].town);
    lv_label_set_text(ui_Database_Output_File, content);

//    if(bPowerStatus == true)
//    { sprintf(message, "%s-%s", Stations.StationNUG[station].countrycode, Stations.StationNUG[station].url);
//      // send countrycode and station url to globe
//      AddToQueueForGlobe(message, MESSAGE_START_THIS_STATION);
//    }
    lv_refr_now(NULL);   
  }
}

void AddFileToQueueForGlobe(uint16_t station)
{ //DataFromDisplay.D_QueueStationIndex = station;
  //Stations.requested = station; 
  //Stations.playing = -1;
  char message[16];
  
  if(station<Stations.count)
  { if(bPowerStatus == true)
    { //AddToQueueForGlobe(Stations.StationNUG[station].url, MESSAGE_START_THIS_FILE);
      sprintf(message, "%d", station);
      AddToQueueForGlobe(message, MESSAGE_START_FILE_BY_INDEX);
      lv_bar_set_value(ui_FilePlayProgressBar, 0, LV_ANIM_OFF);
      lv_refr_now(NULL); 
    }
    //lv_label_set_text(ui_Station_Title, Stations.StationNUG[station].name); // rebuild songname from url
    lv_obj_add_flag(ui_ledconnect, LV_OBJ_FLAG_HIDDEN); 
    lv_label_set_text(ui_Station_Title, ""); // for now
  }
}


void WriteStationsBitmapFile(fs::FS &fs, char* filename)
{ Serial.printf("WriteStationsBitmapFile -> %s\n", filename);
  File bitmap = fs.open(filename, FILE_WRITE);
  if(bitmap) 
  { Serial.printf("WriteStationsBitmapFile opened -> %s\n", filename);
    char *p = (char*) &StationsMap;
    p+=2; // skip filler in structure
    Serial.printf("StationsMap-2 size = %ld\n", sizeof(StationsMap)-2);
    Serial.printf("StationsMap.bmpheader size = %ld\n", sizeof(StationsMap.bmpheader));
    Serial.printf("StationsMap.bmpct size     = %ld\n", sizeof(StationsMap.bmpct));
    Serial.printf("StationsMap.pixeldata size = %ld\n", sizeof(StationsMap.pixeldata));

    int n = 54+8;
    // write header
    while(n)
    { bitmap.write(*p++);
      n--;
    }

    // write file, bottom up
    int w;
    for(n=179;n>=0;n--) // 180 latitudal lines
    { p = (char*)&StationsMap.pixeldata[(n*48)];
      for(w=0;w<48;w++)
      { bitmap.write(*p++);
      }
    }
  }
  bitmap.close();
  Serial.printf("WriteStationsBitmapFile closed -> %s\n", filename);
}


void ReadStationsBitmapFile(fs::FS &fs, char* filename)
{ File bitmap = fs.open(filename, FILE_READ);
  char *p = (char*) &StationsMap;
  p+=2; // skip filler in structure
  if(!bitmap)
  { Serial.printf("No File %s found\n", filename);
    return;
  }
  Serial.printf("File %s opened\n", filename);
  while(bitmap.available())
  { int n = 54+8;
    while(n)
    { char c = bitmap.read();
      *p++ = c;
      n--;
    }

    int w;
    for(n=179;n>=0;n--) // 180 latitudal lines
    { p = (char*)&StationsMap.pixeldata[(n*48)];
      for(w=0;w<48;w++)
      { char c = bitmap.read();
        *p++ = c;
      }
    }
  }
  bitmap.close();
  // WriteStationsBitmapFile(fs, "/stationsmap-copy.bmp"); // test, make a copy
}


void AppendToLogFile(char *filename, char *url)
{ char logtext[256];
  char active_posix_tz[32];
  if(FtpBootState)return; // don't mess around while FTP active..

  if(strcmp(filename, "/Sleeptimer.log") == 0)return; // turn those off for now

  snprintf(logtext, 256, "%d-%s-%d %02d:%02d:%02d ->%s",    (int)datetime.day, monthnames[datetime.month%12],  (int)datetime.year%100, datetime.hour, (int)datetime.minute, (int)datetime.second, url);

  // file creation dates seem to reflect a double TZ correction
  // use UTC to make it a bit more predictable
  //strcpy(active_posix_tz, getenv("TZ")); // crashes display and all?????? make sure TZ is set, first TZ may have not happened yet
  //setenv("TZ", "CUSTOM0:00:00", 1);
  //tzset();

  if(Puck_SD_GB)
  { File logfile = SD_MMC.open(filename, FILE_APPEND);
    if(!logfile)
    { Serial.printf("Could not open Bad Station File %s for append\n", filename);
      logfile = SD_MMC.open(filename, FILE_WRITE);
      if(logfile)
      { logfile.printf("File %s created\n", filename);  
        Serial.printf("File %s created\n", filename);  
      }
      else return;  
    }
    Serial.printf("Log File %s appended with %s\n", filename, logtext);
    logfile.println(logtext);  
    logfile.flush();
    logfile.close();
  }  

  //setenv("TZ", active_posix_tz, 1);
  //tzset();

}

bool FindCountryNameByCode(char *countryname, char*countrycode)
{ uint16_t n=0;
  static char prevcountrycode[3] = "";
  static char prevcountryname[50] = "";
  
  if(strcmp(prevcountrycode, countrycode)==0)
  { strcpy(countryname, prevcountryname);
    return true;
  }

  uint16_t total_countries = sizeof(CountryList) / sizeof(country_info);

  while(n<total_countries)
  { //Serial.printf("CountryList[%d].name = %s countrycode %s\n", n, CountryList[n].name, CountryList[n].code);
    if(strncmp(countrycode, CountryList[n].code, 2)==0)
    { strncpy(prevcountrycode, CountryList[n].code, 2);
      prevcountrycode[2]=0;
      strncpy(prevcountryname, CountryList[n].name, sizeof(prevcountryname) - 1);
      prevcountryname[sizeof(prevcountryname) - 1]=0;
      //Serial.println(countryname);
      strcpy(countryname, prevcountryname);
      return true;
    }
    n++;
  }
  strcpy(countryname, "");
  return false;
}

/*
Squareline Studio notes to self

extra characters in placed in font

settings font create:
fontname : font1
fontsize 20
Bpp 4
ASCII extended 0x20-0x2ff // expand as needed

Symbols 

ext-ascii 0x80-0xFF
¡¢£¤¥¦§¨©ª«¬­®¯°±²³´µ¶·¸¹º»¼½¾¿ÀÁÂÃÄÅÆÇÈÉÊËÌÍÎÏÐÑÒÓÔÕÖ×ØÙÚÛÜÝÞßàáâãäåæçèéêëìíîïðñòóôõö÷øùúûüýþÿ
ext-ascii 0x100-0x1FF
ĀāĂăĄąĆćĈĉĊċČčĎďĐđĒēĔĕĖėĘęĚěĜĝĞğĠġĢģĤĥĦħĨĩ
ext-ascii 0x200-0x27F
ĪīĬĭĮįİıĲĳĴĵĶķĸĹĺĻļĽľĿŀŁłŃńŅņŇňŉŊŋŌōŎŏŐőŒœŔŕŖŗŘřŚśŜŝŞşŠšŢţŤťŦŧŨũŪūŬŭŮůŰűŲųŴŵŶŷŸŹźŻżŽžſƀƁƂƃƄƅƆƇƈƉƊƋ
ext-ascii 0x200-0x27F
ƌƍƎƏƐƑƒƓƔƕƖƗƘƙƚƛƜƝƞƟƠơƢƣƤƥƦƧƨƩƪƫƬƭƮƯưƱƲƳƴƵƶƷƸƹƺƻƼƽƾƿǀǁǂǃǄǅǆǇǈǉǊǋǌǍǎǏǐǑǒǓǔǕǖǗǘǙǚǛǜǝǞǟǠǡǢǣǤǥǦǧǨǩǪǫǬǭǮǯǰǱǲǳǴǵǶǷǸǹǺǻǼǽǾǿ

settings font create:
fontname : montserrat20extended
fontsize 20
Bpp 4
ASCII extended 0x20-0xff

Symbols : paste the above characters collections

*/



char * XXXXAllUpperCase(char *s)
{ int i, slash_count = 0;
  int len = strlen(s);

  // replace all occurencies of '/' with " / "
  // and make all characters uppercase 
  // example "TZ - Asia/Calcutta" becomes -> "TZ - ASIA / CALCUTTA"

  // Serial.println(s);
  // count occurencies of '/'
  for (i = 0; i < len; i++) 
  { if (s[i] == '/')
    slash_count++;
  }

  // new length
  int new_len = len + slash_count * 2;
  s[new_len--] = '\0';

  // Serial.println(new_len);

  // work backwards
  for (i = len - 1; i >= 0; i--) 
  { //Serial.printf("%d = '%c'\n", i, s[i]);
    if (s[i] == '/') 
    { s[new_len--] = ' ';
      s[new_len--] = '/';
      s[new_len--] = ' ';
    } 
    else 
    { s[new_len--] = toupper(s[i]);
    }
  }
  // Serial.println(s);
  return s;
}

char * GetAllUpperCase(char *t, char *s)
{ int i, slash_count = 0;
  int len = strlen(s);

  // replace all occurencies of '/' with " / "
  // and make all characters uppercase 
  // example "TZ - Asia/Calcutta" becomes -> "TZ - ASIA / CALCUTTA"

  // Serial.println(s);
  // count occurencies of '/'
  for (i = 0; i < len; i++) 
  { if (s[i] == '/')
    slash_count++;
  }

  // new length
  int new_len = len + slash_count * 2;
  t[new_len--] = '\0';

  // Serial.println(new_len);

  // work backwards
  for (i = len - 1; i >= 0; i--) 
  { //Serial.printf("%d = '%c'\n", i, s[i]);
    if (s[i] == '/') 
    { t[new_len--] = ' ';
      t[new_len--] = '/';
      t[new_len--] = ' ';
    } 
    else 
    { t[new_len--] = toupper(s[i]);
    }
  }
  // Serial.println(s);
  return t;
}

// Full rebuild, step by step
uint16_t DatabaseFullRebuild(uint16_t state)
{ delay(1000);

  switch(state)
  { case 1:
      state++;
      return state;
      break;
    
    case 10:
      state = 0;
      return state;
      break;

    default:
      state++;
      return state;
      break;

  }

  return 0;

}

/*
rebuild states

1: open rebuildstate.log, read state number and json filesize. if >2 take that state
2: create file, write 3 and size 1000
3: check presence of stationsok.json on sd, increment state to 10
4; if no stationsok.json, download from github stations.json
5: delete stations.json, download stations.json and rename to stationsok.json when done

10 we have a ok json file now. check if size is new/different, 



*/
