Frank-Bemelman/radioglobe-esp32-2025/source/arduino/RadioGlobe-Display-V4/favorites.ino

// favorites
// Select or store a station
// 
// list is loaded from favorites.txt
// and also stored back into favorites.txt
#include "FS.h"
#include "SD_MMC.h"
#include "database.h"
#include "favorites.h"

void playpreset(uint32_t station)
{ if(station<0 || station>=MAX_FAVORITES)return;
  if(strlen(Stations.StationNUG[station+MAX_STATIONS].url)>0) // only respond to loaded buttons
  { Serial.printf("Globe request Favorites Preset station %s under Preset %d\n", Stations.StationNUG[station+MAX_STATIONS].name, station);
    AddStationToQueueForGlobe(station+MAX_STATIONS); // presets come just after the regular list of stations
    SetLed(station, UI_THEME_COLOR_RED);
    beepforMs(50);
  }  
}

void station1234(lv_event_t * e, uint16_t station)
{ static uint16_t longpressed;
  lv_event_code_t event_code = lv_event_get_code(e);

  if(event_code == LV_EVENT_LONG_PRESSED_REPEAT && !bMusicMode) 
  { //Serial.printf("hey-favorites-Station->event=%s %d\n", "LV_EVENT_LONG_PRESSED, longpressed");
    longpressed++;
    if(longpressed == 5)
    { if(Stations.playing >=0)
      { // all in one array
        strcpy(Stations.StationNUG[station+MAX_STATIONS].name, Stations.StationNUG[Stations.playing].name);
        strcpy(Stations.StationNUG[station+MAX_STATIONS].url, Stations.StationNUG[Stations.playing].url);
        Stations.StationNUG[station+MAX_STATIONS].gps_ns = Stations.StationNUG[Stations.playing].gps_ns;
        Stations.StationNUG[station+MAX_STATIONS].gps_ew = Stations.StationNUG[Stations.playing].gps_ew;
        strcpy(Stations.StationNUG[station+MAX_STATIONS].town, Stations.StationNUG[Stations.playing].town);
        strcpy(Stations.StationNUG[station+MAX_STATIONS].countrycode, Stations.StationNUG[Stations.playing].countrycode);
        strcpy(Stations.StationNUG[station+MAX_STATIONS].countryname, Stations.StationNUG[Stations.playing].countryname);
        SetLed(station, UI_THEME_COLOR_GREEN); // station is already playing, so set led to green
        
        if(station==0)
        { lv_label_set_text(ui_StationPresetName1, Stations.StationNUG[station+MAX_STATIONS].name); 
        }  
        if(station==1)
        { lv_label_set_text(ui_StationPresetName2, Stations.StationNUG[station+MAX_STATIONS].name); 
        }  
        if(station==2)
        { lv_label_set_text(ui_StationPresetName3, Stations.StationNUG[station+MAX_STATIONS].name); 
        }  
        if(station==3)
        { lv_label_set_text(ui_StationPresetName4, Stations.StationNUG[station+MAX_STATIONS].name); 
        }  

        Serial.printf("Favorites STORE station %s under Preset %d\n", Stations.StationNUG[station+MAX_STATIONS].name, station);
        SaveFavorites();
        //SaveFavoritesToEEprom(); // makes display go funny
        beepforMs(1000);
      }
    }  
  }

  if(event_code == LV_EVENT_CLICKED) 
  { if(longpressed==0)
    { if(strlen(Stations.StationNUG[station+MAX_STATIONS].url)>0) // only respond to loaded buttons
      { Serial.printf("64 favorites.ino - Favorites Select station %s under Preset %d\n", Stations.StationNUG[station+MAX_STATIONS].name, station);
        AddStationToQueueForGlobe(station+MAX_STATIONS); // presets come just after the regular list of stations
        SetLed(station, UI_THEME_COLOR_RED);
      
        // place flag icon in vertical position
        int16_t yc = (station * 70) - 104;
        lv_obj_set_y(ui_PresetFlag, yc);  // -104 -34 34 104 

        lv_label_set_text(ui_Station_Name, Stations.StationNUG[station+MAX_STATIONS].name);
        beepforMs(50);
      }  
    }
    longpressed = 0;
  }
}

void station1(lv_event_t * e)
{  station1234(e, 0);
}

void station2(lv_event_t * e)
{  station1234(e, 1);
}

void station3(lv_event_t * e)
{  station1234(e, 2);
}

void station4(lv_event_t * e)
{  station1234(e, 3);
}

// just save the favorites to file
void SaveFavorites(void)
{ File favfile;
  char favfilename[] = {"/favorites.txt"};
  char *p;
  char sometext[128];

  if(Puck_SD_GB == 0)return; // no card


  SD_MMC.remove(favfilename); // delete old file
  favfile = SD_MMC.open(favfilename, FILE_WRITE);
  if(favfile)
  { for(int16_t n = 0; n<(MAX_FAVORITES+MAX_HOMES); n++)
    { if((p=strchr(Stations.StationNUG[n+MAX_STATIONS].name, '\n'))!=0)*p=0;
      if((p=strchr(Stations.StationNUG[n+MAX_STATIONS].url, '\n'))!=0)*p=0;
      if((p=strchr(Stations.StationNUG[n+MAX_STATIONS].name, '\r'))!=0)*p=0;
      if((p=strchr(Stations.StationNUG[n+MAX_STATIONS].url, '\r'))!=0)*p=0;
      sprintf(sometext, "\"name\": \"%s\"", Stations.StationNUG[n+MAX_STATIONS].name);
      favfile.println(sometext);  
      sprintf(sometext, "\"url\": \"%s\"", Stations.StationNUG[n+MAX_STATIONS].url);
      favfile.println(sometext);  
      sprintf(sometext, "\"gps\": \"%f,%f\"", Stations.StationNUG[n+MAX_STATIONS].gps_ns, Stations.StationNUG[n+MAX_STATIONS].gps_ew); // write gps to file
      favfile.println(sometext);  
      sprintf(sometext, "\"town\": \"%s\"", Stations.StationNUG[n+MAX_STATIONS].town);
      favfile.println(sometext);  
      sprintf(sometext, "\"countrycode\": \"%s\"", Stations.StationNUG[n+MAX_STATIONS].countrycode);
      favfile.println(sometext);  
      sprintf(sometext, "\"countryname\": \"%s\"", Stations.StationNUG[n+MAX_STATIONS].countryname);
      favfile.println(sometext);  
    }  
  }
  favfile.close();
 
}

// just save the favorites to Eeprom
void SaveFavoritesToEEprom(void)
{ int16_t station;
  for(station = 0; station<MAX_FAVORITES+MAX_HOMES; station++)
  { memcpy(&DisplaySettings.stationnug[station], &Stations.StationNUG[MAX_STATIONS+station], sizeof(Stations.StationNUG[0]));
  }
  SaveDisplaySettings();
  Serial.println("Finished saving favorites/presets to EEprom");
}


void LoadFavorites(void)
{ File favfile;
  char favfilename[] = {"/favorites.txt"};
  char *p;
  char text[140];  
  int16_t favcount;

  for(favcount=0; favcount<5; favcount++)
  { strcpy(Stations.StationNUG[favcount+MAX_STATIONS].name, "");
    strcpy(Stations.StationNUG[favcount+MAX_STATIONS].url, "");
    strcpy(Stations.StationNUG[favcount+MAX_STATIONS].url, "");
    Stations.StationNUG[favcount+MAX_STATIONS].gps_ns = 0; 
    Stations.StationNUG[favcount+MAX_STATIONS].gps_ew = 0; 
    strcpy(Stations.StationNUG[favcount+MAX_STATIONS].town, "");
    strcpy(Stations.StationNUG[favcount+MAX_STATIONS].countrycode, "??");
    strcpy(Stations.StationNUG[favcount+MAX_STATIONS].countryname, "");
  }

  if(Puck_SD_GB == 0)return; // no card


  favfile = SD_MMC.open(favfilename, FILE_READ);
  if(favfile)
  { favcount = -1;
    while(favfile.available()) 
    { String data = favfile.readStringUntil('\n');
      strcpy(text, data.c_str());
      if((p=strchr(text, '\n'))!=0)*p=0;
      if((p=strchr(text, '\r'))!=0)*p=0;
      if((p = strrchr(text, '\"')) != 0)*p=0; // get rid of the last "
      if((p = strstr(text, "\"name\": ")) != 0) 
      { favcount++;
        p+=9; // jump forward to start of name
        strncpy(Stations.StationNUG[favcount+MAX_STATIONS].name, p, sizeof(Stations.StationNUG[0].name));
        Stations.StationNUG[favcount+MAX_STATIONS].name[sizeof(Stations.StationNUG[0].name)-1]=0;
      }

      //Serial.printf("Preset % d text = <%s>\n", favcount, text);
      
      if(favcount>=0 && favcount<MAX_FAVORITES+MAX_HOMES) // max 4 presets + 1 home location
      {
        if((p = strstr(text, "\"url\": ")) != 0) 
        { p+=8; // jump forward to start of name
          strcpy(Stations.StationNUG[favcount+MAX_STATIONS].url, p);
        }
        if((p = strstr(text, "\"gps\": ")) != 0) 
        { p+=8; // jump forward to start of name
          sscanf(p, "%f,%f", &Stations.StationNUG[favcount+MAX_STATIONS].gps_ns, &Stations.StationNUG[favcount+MAX_STATIONS].gps_ew);
        }
        if((p = strstr(text, "\"town\": ")) != 0) 
        { p+=9; // jump forward to start of name
          strcpy(Stations.StationNUG[favcount+MAX_STATIONS].town, p);
        }
        if((p = strstr(text, "\"countrycode\": ")) != 0) 
        { p+=16; // jump forward to start of name
          strncpy(Stations.StationNUG[favcount+MAX_STATIONS].countrycode, p, 2);
          Stations.StationNUG[favcount+MAX_STATIONS].countrycode[2]=0;
          //Serial.printf("Preset % d countrycode = <%s>\n", favcount, Stations.StationNUG[favcount+MAX_STATIONS].countrycode);
          //if(favcount<4)SetFlag(Stations.StationNUG[favcount+MAX_STATIONS].countrycode, favcount+1); // sets the flag in the preset screen but was too memory costly
        }
        if((p = strstr(text, "\"countryname\": ")) != 0) 
        { p+=16; // jump forward to start of name
          strncpy(Stations.StationNUG[favcount+MAX_STATIONS].countryname, p, 49);
          Stations.StationNUG[favcount+MAX_STATIONS].countryname[49]=0;
          //Serial.printf("Preset % d countryname = <%s>\n", favcount, Stations.StationNUG[favcount+MAX_STATIONS].countryname);
        }
      }
    }
    for(int16_t station = 0; station<MAX_FAVORITES; station++)
    { //Serial.printf("Loaded Station %d = %s\n", station, Stations.StationNUG[station+MAX_STATIONS].name);
      if(station==0)lv_label_set_text(ui_StationPresetName1, Stations.StationNUG[0+MAX_STATIONS].name); 
      if(station==1)lv_label_set_text(ui_StationPresetName2, Stations.StationNUG[1+MAX_STATIONS].name); 
      if(station==2)lv_label_set_text(ui_StationPresetName3, Stations.StationNUG[2+MAX_STATIONS].name); 
      if(station==3)lv_label_set_text(ui_StationPresetName4, Stations.StationNUG[3+MAX_STATIONS].name); 
    } 
    favfile.close();
  }
  // turn of preset leds
  SetLed(1, 0);
  SetLed(2, 0);
  SetLed(3, 0);
  SetLed(4, 0);
  Lvgl_Loop();
  
  Serial.println("Finished loading favorites/presets from SD");


}


void LoadFavoritesFromEEprom(void)
{ int16_t station;

  for(station = 0; station<MAX_FAVORITES+MAX_HOMES; station++)
  { memcpy(&Stations.StationNUG[MAX_STATIONS+station], &DisplaySettings.stationnug[station], sizeof(Stations.StationNUG[0]));
    if(station==0)lv_label_set_text(ui_StationPresetName1, DisplaySettings.stationnug[0].name); 
    if(station==1)lv_label_set_text(ui_StationPresetName2, DisplaySettings.stationnug[1].name); 
    if(station==2)lv_label_set_text(ui_StationPresetName3, DisplaySettings.stationnug[2].name); 
    if(station==3)lv_label_set_text(ui_StationPresetName4, DisplaySettings.stationnug[3].name); 
  }
  // turn of preset leds
  SetLed(1, 0);
  SetLed(2, 0);
  SetLed(3, 0);
  SetLed(4, 0);
  Lvgl_Loop();
  Serial.println("Finished loading favorites/presets from EEprom");
}





void SetLed(int16_t preset, int16_t themecolor)
{ static int16_t ledColor[4];
  
  if(preset>3) return;

  ledColor[preset] = themecolor;

  if(!ledColor[0] && !ledColor[1] && !ledColor[2] && !ledColor[3]) // all leds off
  { lv_obj_add_flag(uic_PresetLed, LV_OBJ_FLAG_HIDDEN);
    return;
  }

  if(ledColor[preset]) 
  { lv_obj_set_y(uic_PresetLed, (preset * 70) - 105);  // -105 -35 35 105 
   
    if(themecolor == UI_THEME_COLOR_RED)
    { ui_object_set_themeable_style_property(uic_PresetLed, LV_PART_MAIN | LV_STATE_DEFAULT, LV_STYLE_IMG_RECOLOR, _ui_theme_color_red);
      ui_object_set_themeable_style_property(uic_PresetLed, LV_PART_MAIN | LV_STATE_DEFAULT, LV_STYLE_IMG_RECOLOR_OPA, _ui_theme_alpha_red);
    }
    if(themecolor == UI_THEME_COLOR_GREEN)
    { ui_object_set_themeable_style_property(uic_PresetLed, LV_PART_MAIN | LV_STATE_DEFAULT, LV_STYLE_IMG_RECOLOR, _ui_theme_color_green);
      ui_object_set_themeable_style_property(uic_PresetLed, LV_PART_MAIN | LV_STATE_DEFAULT, LV_STYLE_IMG_RECOLOR_OPA, _ui_theme_alpha_green);
    }  
    lv_obj_clear_flag(uic_PresetLed, LV_OBJ_FLAG_HIDDEN);

    // turn all other virtual leds off
    for(int16_t n=0; n<4; n++)
    { if(n!=preset)ledColor[n]=0;
    }   
  }  
}
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
