Frank-Bemelman/radioglobe-esp32-2025/source/arduino/RadioGlobe-Display-V4/franks-esp-now.ino

/*
  Credits for this work from which I borrowed a lot of code from:
  Rui Santos & Sara Santos - Random Nerd Tutorials
  Complete project details at https://RandomNerdTutorials.com/esp-now-two-way-communication-esp32/
  Permission is hereby granted, free of charge, to any person obtaining a copy of this software and associated documentation files.
  The above copyright notice and this permission notice shall be included in all copies or substantial portions of the Software.
*/

#include <WiFi.h>
#include <esp_now.h>
#include "franks-esp-now.h"

// Test stuff
// REPLACE WITH THE MAC Address of globe
// which is 94:b5:55:2b:2a:d4 (broken one, diode])
// uint8_t broadcastAddress[] = {0x94, 0xB5, 0x55, 0x2B, 0x2A, 0xD4};
// 0c:b8:15:c3:e4:10 // also broken
// e0:5a:1b:e2:f0:68 wroom without double antenna = {0xE0, 0x5A, 0x1B, 0xE2, 0xF0, 0x68};
// 30:ed:a0:b8:c6:4c esp32-s3-N16R8 = {0x30, 0xED, 0xA0, 0xB8, 0xC6, 0x4C}; // first test, pins soldered upwards
// 30:ED:A0:B7:29:10 esp32-s3-N16R8 = {0x30, 0xED, 0xA0, 0xB7, 0x29, 0x10}; // 2nd protofirst test, pins soldered downwards
// uint8_t broadcastAddress[] = {0x30, 0xED, 0xA0, 0xB8, 0xC6, 0x4C};
// uint8_t broadcastAddress[] = {0x30, 0xED, 0xA0, 0xB7, 0x29, 0x10};
// uint8_t broadcastGlobeMac[] = {0x98, 0xA3, 0x16, 0xE6, 0x9A, 0x1C}; 
// uint8_t GlobeMac[] = {0x01, 0x02, 0x03, 0x04, 0x05, 0x06}; 

esp_now_peer_info_t peerInfo = {};
const esp_now_peer_info_t *masterNode = &peerInfo;
//int dataSent = 0;
//int dataReceived = 0;

int ms_sleep = 0;
esp_err_t sendResult;

bool bSendAckToGlobe = false;

#define HIGHEST_CHANNEL	13    //Set according to country
#define LOWEST_CHANNEL  1

void OnDataSent(const esp_now_send_info_t *tx_info, esp_now_send_status_t status);
void OnDataRecv(const esp_now_recv_info_t *rx_info, const uint8_t *incomingData, int len);

// Callback when data is sent
volatile bool bWasTransmitted = false;
volatile bool bWasReceived = false;
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
